NoahLock10/404-Ionic/Micro Controller Subsystem/hex converter.PNG

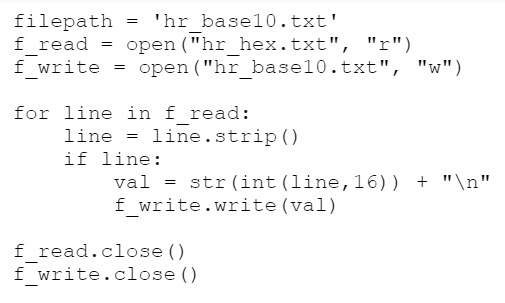
Micro Controller Subsystem/hex converter.PNG
