NoahLock10/404-Ionic/Micro Controller Subsystem/temperature.PNG

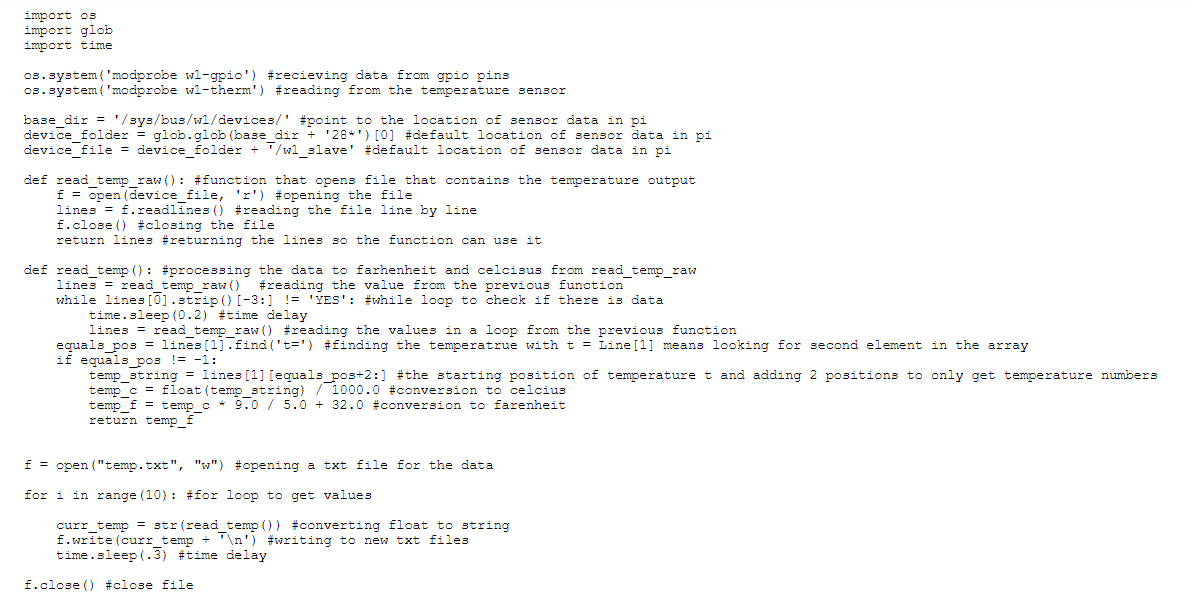
Micro Controller Subsystem/temperature.PNG
